MrChunckuee-Electronics/ACS722_LowCurrentSensor_Project/assets/2 ACS722_Low_Current_Sensor_Top.PNG

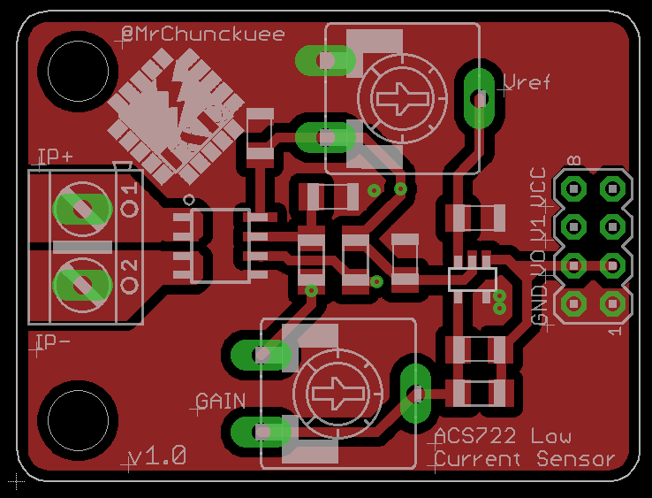
assets/2 ACS722_Low_Current_Sensor_Top.PNG
