MrChunckuee-Electronics/ACS722_LowCurrentSensor_Project/assets/5 ACS722_Low_Current_Sensor_Serigrafia_Bottom.PNG

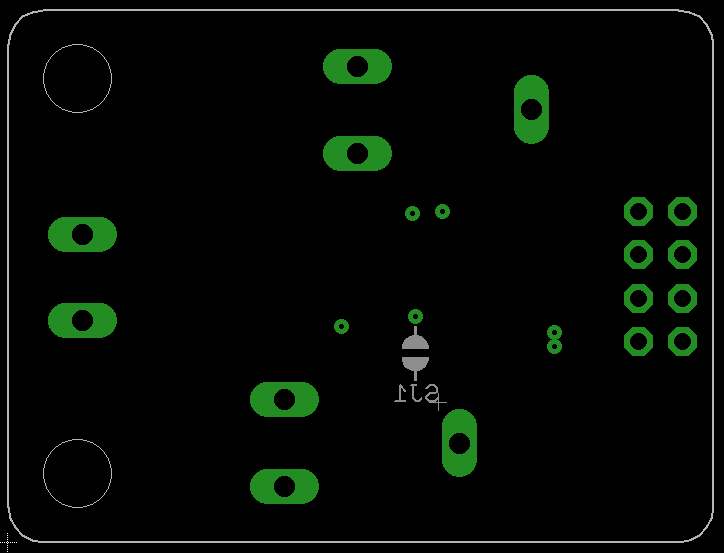
assets/5 ACS722_Low_Current_Sensor_Serigrafia_Bottom.PNG
